customMK/Bonsai-C/C3/img/Bonsai C front.png

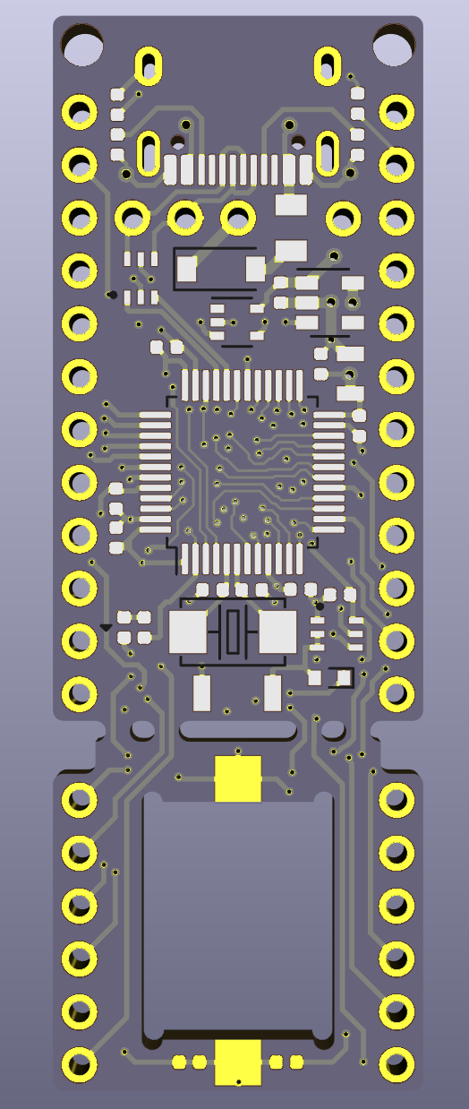
C3/img/Bonsai C front.png
