customMK/Bonsai-C/C3/img/Bonsai C layers.png

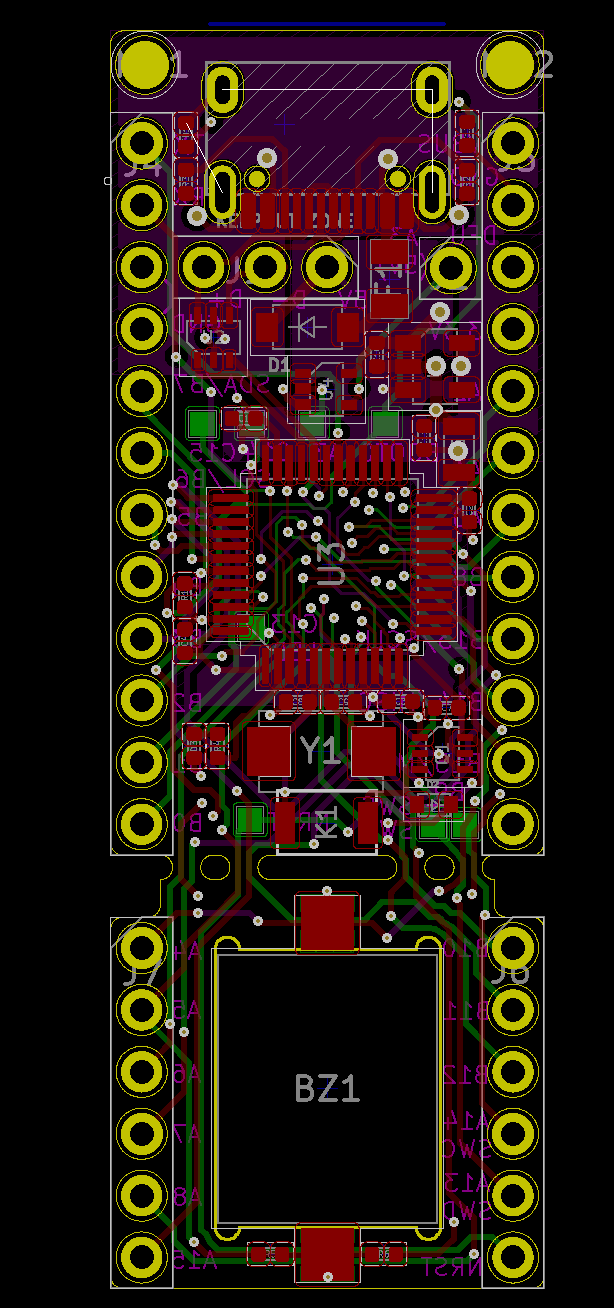
C3/img/Bonsai C layers.png
